jamesjnadeau/watchy-ref-counter/RefCounter/RefMenu.cpp

// ---------------------------------------------------------------------------
// The settings menu.
//
// The shape of this -- a highlighted list, UP and DOWN to move, MENU to
// select, BACK to leave, a set-time screen whose current field blinks, a WiFi
// access point for entering credentials, an NTP sync that reports what it did
// -- follows the reference Watchy firmware, sqfmi/Watchy (MIT licence), by way
// of credit. The code is this project's own; nothing is linked from or copied
// out of that repo.
//
// Deliberate differences from the reference:
//   - no "Show Accelerometer"; nothing on a play clock reads the sensor
//   - no "Vibrate Motor" buzz test; the buzzer proves itself every countdown
//   - "Sync NTP" is only listed once WiFi credentials have been saved, since
//     with none stored it could only ever report a failure
//   - "Sync BT" has no counterpart there at all: the watch advertises the
//     standard Current Time Service and a phone writes the time into it
//   - colours follow DARK_MODE rather than being fixed black on white
//   - actions never redraw the menu themselves; open() owns that
//   - NTP goes through the ESP32 core's SNTP client, not a separate library
//   - the digits reuse this project's seven-segment drawing, not a font
//   - "TZ" and "DST" have no counterpart there; the reference firmware takes
//     its offset from a compile-time constant
// ---------------------------------------------------------------------------

#include "RefMenu.h"

#include <WiFi.h>
#include <WiFiManager.h>

#include "Buttons.h"
#include "Buzzer.h"
#include "RefBleTime.h"
#include "RefDisplay.h"
#include "RefMenuItems.h"
#include "RefPanel.h"
#include "RefSport.h"
#include "RefWifi.h"
#include "RefZone.h"
#include "board.h"
#include "settings.h"

namespace RefMenu {
namespace {

auto &display = RefPanel::display;

const int16_t MENU_ROW_H = 25;

// Rows that fit on the panel at MENU_ROW_H. Both sync rows on offer makes the
// list two rows longer than this, so drawMenu scrolls a window over it, the
// way pickTimeZone does over the zones; strip both conditional rows away and
// it fits exactly.
const uint8_t MENU_VISIBLE = 7;

// Whether the Bluetooth row is worth offering. A build with no BLE, or with
// BT_TIME_SYNC off, leaves it out entirely.
bool btAvailable() { return RefBleTime::supported(); }

// The rows currently on offer, in order, and how many there are. Rebuilt on
// the way in and after every action, because "Setup WiFi" can add or remove
// "Sync NTP" underneath the user.
uint8_t visible[ITEM_COUNT];
uint8_t visibleCount = 0;

// Top of the visible window. Lives outside drawMenu so it survives the redraws
// that follow an action, and is reset in open() so the menu never comes up
// scrolled from last time.
uint8_t menuTop = 0;

// "UTC-5", or "UTC-9:30" if a zone ever needs it.
void formatOffset(char *buf, size_t n, long seconds) {
  const char sign = seconds < 0 ? '-' : '+';
  long mag = seconds < 0 ? -seconds : seconds;
  if (mag > 24L * 3600L) {
    mag = 24L * 3600L; // no real zone is further out, and this bounds the width
  }
  const int hours = (int)(mag / 3600);
  const int mins  = (int)((mag % 3600) / 60);
  if (mins == 0) {
    snprintf(buf, n, "UTC%c%d", sign, hours);
  } else {
    snprintf(buf, n, "UTC%c%d:%02d", sign, hours, mins);
  }
}

enum SetField : int8_t { SET_HOUR, SET_MINUTE, SET_YEAR, SET_MONTH, SET_DAY };

bool pressed(uint8_t pin) { return digitalRead(pin) == BTN_PRESSED_LEVEL; }

void claimButtons() {
  pinMode(PIN_BTN_MENU, INPUT);
  pinMode(PIN_BTN_BACK, INPUT);
  pinMode(PIN_BTN_UP, INPUT);
  pinMode(PIN_BTN_DOWN, INPUT);
}

void beginTextScreen() {
  display.setFullWindow();
  display.fillScreen(THEME_BG);
  display.setFont(&FreeMonoBold9pt7b);
  display.setTextColor(THEME_FG);
  display.setCursor(0, 20);
}

void printTwo(int v) {
  if (v < 10) {
    display.print("0");
  }
  display.print(v);
}

// `slot` is a position in `visible`, not an Item id.
void drawMenu(uint8_t slot, bool partial) {
  // Keep the highlighted row inside the window, and never scroll past the end.
  if (slot < menuTop) {
    menuTop = slot;
  } else if (slot >= menuTop + MENU_VISIBLE) {
    menuTop = (uint8_t)(slot - MENU_VISIBLE + 1);
  }
  if (visibleCount > MENU_VISIBLE &&
      menuTop > (uint8_t)(visibleCount - MENU_VISIBLE)) {
    menuTop = (uint8_t)(visibleCount - MENU_VISIBLE);
  } else if (visibleCount <= MENU_VISIBLE) {
    menuTop = 0;
  }

  display.setFullWindow();
  display.fillScreen(THEME_BG);
  display.setFont(&FreeMonoBold9pt7b);

  char label[ITEM_LABEL_MAX];
  int16_t x1, y1;
  uint16_t w, h;
  for (uint8_t row = 0; row < MENU_VISIBLE && menuTop + row < visibleCount;
       row++) {
    const uint8_t s = (uint8_t)(menuTop + row);
    itemLabel(visible[s], label, sizeof(label));
    const int16_t yPos = MENU_ROW_H + (MENU_ROW_H * row);
    display.setCursor(0, yPos);
    if (s == slot) {
      display.getTextBounds(label, 0, yPos, &x1, &y1, &w, &h);
      display.fillRect(x1 - 1, y1 - 10, DISPLAY_WIDTH, h + 15, THEME_FG);
      display.setTextColor(THEME_BG);
    } else {
      display.setTextColor(THEME_FG);
    }
    display.println(label);
  }
  display.display(partial);
}

void showAbout(RefClock &refClock) {
  beginTextScreen();

  display.print("Ref Counter ");
  display.println(REF_COUNTER_VERSION);
  display.print("Board: ");
  display.println(BOARD_NAME);
  display.print("Batt: ");
  display.print(refClock.batteryVolts(), 2);
  display.println("V");

  struct tm now;
  const bool haveTime = refClock.localNow(now);
  display.print("Now: ");
  if (!haveTime) {
    display.println("not set");
  } else {
    display.print(now.tm_year + 1900);
    display.print("/");
    printTwo(now.tm_mon + 1);
    display.print("/");
    printTwo(now.tm_mday);
    display.print(" ");
    printTwo(now.tm_hour);
    display.print(":");
    printTwo(now.tm_min);
    display.println();
  }

  const time_t nowEpoch = haveTime ? refClock.rtc().epoch() : 0;
  const time_t boot     = refClock.bootEpoch();
  if (boot != 0 && nowEpoch > boot) {
    const uint32_t up = (uint32_t)(nowEpoch - boot);
    display.print("Up: ");
    display.print(up / 86400);
    display.print("d");
    display.print((up % 86400) / 3600);
    display.print("h");
    display.print((up % 3600) / 60);
    display.println("m");
  }

  // Which source last set the clock matters as much as when: an hour out
  // after a Bluetooth sync means the phone's zone and the watch's disagree,
  // which is a different fault from a stale NTP sync.
  const time_t sync = refClock.lastSyncEpoch();
  const char *how   = "";
  switch (refClock.lastSyncSource()) {
  case RefClock::SYNC_NTP: how = " NTP"; break;
  case RefClock::SYNC_BT:  how = " BT"; break;
  default: break;
  }
  if (sync == 0) {
    display.println("Sync: never");
  } else if (nowEpoch > sync) {
    char line[24];
    snprintf(line, sizeof(line), "Sync: %uh ago%s",
             (unsigned)((uint32_t)(nowEpoch - sync) / 3600), how);
    display.println(line);
  }

  const char *rtcName = "none";
  switch (refClock.rtc().kind()) {
  case RefRtc::PCF8563: rtcName = "PCF8563"; break;
  case RefRtc::RV3028:  rtcName = "RV-3028"; break;
  default: break;
  }
  display.print("RTC: ");
  display.println(rtcName);

  // The offset actually in force, which is the only way to confirm from the
  // watch that the daylight saving rule did what was expected of it.
  char offset[12];
  formatOffset(offset, sizeof(offset), refClock.utcOffsetSeconds());
  display.print(RefZone::name(RefZone::index()));
  display.print(" ");
  display.print(refClock.zoneAbbrev());
  display.print(" ");
  display.println(offset);

  display.display(false); // full refresh
}

// The sport picker. Same shape as the zone picker below: a scrolling window of
// rows, MENU to take the highlighted one, BACK to leave the stored one alone,
// and a timeout so a menu opened by accident cannot strand anyone mid-game.
void pickSport() {
  const int16_t ROW_H   = 22;
  const uint8_t VISIBLE = 7;
  const int16_t FIRST_Y = 22;
  const int16_t RULE_Y  = 164;
  const uint8_t total   = RefSport::count();

  uint8_t index = RefSport::index();
  uint8_t top   = index < VISIBLE ? 0 : (uint8_t)(index - VISIBLE + 1);

  claimButtons();
  display.setFullWindow();

  bool first = true;
  uint32_t lastActivity = millis();
  while (millis() - lastActivity < MENU_TIMEOUT_MS) {
    // Keep the highlighted row inside the visible window.
    if (index < top) {
      top = index;
    } else if (index >= top + VISIBLE) {
      top = (uint8_t)(index - VISIBLE + 1);
    }

    display.fillScreen(THEME_BG);
    display.setFont(&FreeMonoBold9pt7b);

    // "Custom    199/199" is the widest row, 17 glyphs of the 18 that fit --
    // Custom is reachable at its ceiling, which none of the fixed presets are.
    char row[24];
    for (uint8_t slot = 0; slot < VISIBLE && top + slot < total; slot++) {
      const uint8_t s       = (uint8_t)(top + slot);
      const int16_t yPos    = FIRST_Y + ROW_H * slot;
      const RefSport::Preset p = RefSport::preset(s);
      snprintf(row, sizeof(row), "%-9s %u/%u", p.name, (unsigned)p.longSeconds,
               (unsigned)p.shortSeconds);

      if (s == index) {
        display.fillRect(0, yPos - 17, DISPLAY_WIDTH, ROW_H - 1, THEME_FG);
        display.setTextColor(THEME_BG);
      } else {
        display.setTextColor(THEME_FG);
      }
      display.setCursor(2, yPos);
      display.print(row);
    }

    display.setTextColor(THEME_FG);
    display.drawFastHLine(0, RULE_Y, DISPLAY_WIDTH, THEME_FG);

    const RefSport::Preset sel = RefSport::preset(index);

    display.setCursor(2, 180);
    display.print(sel.description);

    char counter[10];
    snprintf(counter, sizeof(counter), "%u/%u", (unsigned)(index + 1),
             (unsigned)total);
    // FreeMonoBold9pt7b advances 11 pixels a glyph, so right-aligning is
    // arithmetic rather than a getTextBounds round trip.
    display.setCursor(DISPLAY_WIDTH - 2 - (int16_t)(strlen(counter) * 11), 180);
    display.print(counter);

    // The warning marks, which are the half of a preset the rows have no room
    // for. The final-countdown value is deliberately not here: it is 5 for
    // every fixed preset, so it never tells two of them apart, and the one
    // preset that can change it shows it spelled out on its own editor screen.
    // Three values would need a one-letter label to fit the panel at 199.
    char marks[24];
    snprintf(marks, sizeof(marks), "warn %u/%u",
             (unsigned)sel.warnAtSeconds, (unsigned)sel.warn2AtSeconds);
    display.setCursor(2, 196);
    display.print(marks);

    display.display(!first); // full refresh on the way in, partial to scroll
    first = false;

    // Poll until something happens, so a settled screen is not redrawn on a
    // loop for no reason.
    while (millis() - lastActivity < MENU_TIMEOUT_MS) {
      if (pressed(PIN_BTN_MENU)) {
        RefSport::setIndex(index);
        Buzzer::pulse(BUZZ_CONFIRM_MS);
        Buttons::waitForRelease();
        return;
      }
      if (pressed(PIN_BTN_BACK)) {
        Buttons::waitForRelease();
        return; // leave the stored sport alone
      }
      if (pressed(PIN_BTN_UP)) {
        index = (index == 0) ? (uint8_t)(total - 1) : (uint8_t)(index - 1);
        lastActivity = millis();
        break;
      }
      if (pressed(PIN_BTN_DOWN)) {
        index = (uint8_t)((index + 1) % total);
        lastActivity = millis();
        break;
      }
      delay(BUTTON_POLL_MS);
    }
  }
}

// The zone picker. Eleven zones do not fit on a 200 pixel panel, so this
// scrolls a seven row window and reports the highlighted zone underneath.
void pickTimeZone() {
  const int16_t ROW_H     = 22;
  const uint8_t VISIBLE   = 7;
  const int16_t FIRST_Y   = 22;
  const int16_t RULE_Y    = 164;
  const uint8_t total     = RefZone::count();

  uint8_t index = RefZone::index();
  uint8_t top   = index < VISIBLE ? 0 : (uint8_t)(index - VISIBLE + 1);

  claimButtons();
  display.setFullWindow();

  bool first = true;
  uint32_t lastActivity = millis();
  while (millis() - lastActivity < MENU_TIMEOUT_MS) {
    // Keep the highlighted row inside the visible window.
    if (index < top) {
      top = index;
    } else if (index >= top + VISIBLE) {
      top = (uint8_t)(index - VISIBLE + 1);
    }

    display.fillScreen(THEME_BG);
    display.setFont(&FreeMonoBold9pt7b);

    char row[24], offset[12];
    for (uint8_t slot = 0; slot < VISIBLE && top + slot < total; slot++) {
      const uint8_t z    = (uint8_t)(top + slot);
      const int16_t yPos = FIRST_Y + ROW_H * slot;
      formatOffset(offset, sizeof(offset),
                   RefZone::standardOffsetMinutes(z) * 60L);
      snprintf(row, sizeof(row), "%-8s %s", RefZone::name(z), offset);

      if (z == index) {
        display.fillRect(0, yPos - 17, DISPLAY_WIDTH, ROW_H - 1, THEME_FG);
        display.setTextColor(THEME_BG);
      } else {
        display.setTextColor(THEME_FG);
      }
      display.setCursor(2, yPos);
      display.print(row);
    }

    display.setTextColor(THEME_FG);
    display.drawFastHLine(0, RULE_Y, DISPLAY_WIDTH, THEME_FG);

    // Abbreviations on the left, position in the list on the right. The
    // standard offset is on the row itself, so this is where the reader finds
    // out whether the zone shifts at all.
    char abbrev[20];
    if (RefZone::observesDst(index)) {
      snprintf(abbrev, sizeof(abbrev), "%s/%s", RefZone::standardAbbrev(index),
               RefZone::daylightAbbrev(index));
    } else {
      snprintf(abbrev, sizeof(abbrev), "%s, no DST",
               RefZone::standardAbbrev(index));
    }
    display.setCursor(2, 180);
    display.print(abbrev);

    char counter[10];
    snprintf(counter, sizeof(counter), "%u/%u", (unsigned)(index + 1),
             (unsigned)total);
    // FreeMonoBold9pt7b advances 11 pixels a glyph, so right-aligning is
    // arithmetic rather than a getTextBounds round trip.
    display.setCursor(DISPLAY_WIDTH - 2 - (int16_t)(strlen(counter) * 11), 180);
    display.print(counter);

    display.setCursor(2, 196);
    display.print(RefZone::region(index));

    display.display(!first); // full refresh on the way in, partial to scroll
    first = false;

    // Poll until something happens, so a settled screen is not redrawn on a
    // loop for no reason.
    while (millis() - lastActivity < MENU_TIMEOUT_MS) {
      if (pressed(PIN_BTN_MENU)) {
        RefZone::setIndex(index);
        Buzzer::pulse(BUZZ_CONFIRM_MS);
        Buttons::waitForRelease();
        return;
      }
      if (pressed(PIN_BTN_BACK)) {
        Buttons::waitForRelease();
        return; // leave the stored zone alone
      }
      if (pressed(PIN_BTN_UP)) {
        index = (index == 0) ? (uint8_t)(total - 1) : (uint8_t)(index - 1);
        lastActivity = millis();
        break;
      }
      if (pressed(PIN_BTN_DOWN)) {
        index = (uint8_t)((index + 1) % total);
        lastActivity = millis();
        break;
      }
      delay(BUTTON_POLL_MS);
    }
  }
}

// MENU steps forward through the fields and commits past the last one, BACK
// steps back, UP and DOWN change the value under the cursor. The field being
// edited blinks, which is what tells you where you are.
//
// Times out after MENU_TIMEOUT_MS with nothing pressed, and a timeout leaves
// the clock exactly as it was. This screen repaints twice a second, so one
// opened by accident and then left alone would otherwise hold the watch there
// -- refreshing the panel the whole time -- until the battery went flat.
void setTime(RefClock &refClock) {
  struct tm current;
  if (!refClock.localNow(current)) {
    // Nothing sensible on the clock yet, so start from a fixed point rather
    // than from whatever the chip powered up holding.
    current          = {};
    current.tm_year  = 125; // 2025
    current.tm_mon   = 0;
    current.tm_mday  = 1;
  }

  int hour   = current.tm_hour;
  int minute = current.tm_min;
  int year   = (current.tm_year + 1900) % 100;
  int month  = current.tm_mon + 1;
  int day    = current.tm_mday;

  int8_t field     = SET_HOUR;
  bool   blink     = false;
  // Only true on the MENU-past-last-field path below, so a timeout -- which
  // also falls out of the loop -- can never reach the RTC write at the bottom.
  bool   committed = false;

  claimButtons();
  display.setFullWindow();

  const int16_t pairY = 40;
  const int16_t leftX = 4;
  const int16_t rightX = DISPLAY_WIDTH - RefDisplay::DIGIT_PAIR_W - 4;

  uint32_t lastActivity = millis();
  while (millis() - lastActivity < MENU_TIMEOUT_MS) {
    const bool menuDown = pressed(PIN_BTN_MENU);
    const bool backDown = pressed(PIN_BTN_BACK);
    const bool upDown   = pressed(PIN_BTN_UP);
    const bool downDown = pressed(PIN_BTN_DOWN);
    // Any press counts as activity, even one that turns out to be inert (BACK
    // on the first field): a user still working the buttons is not idle.
    if (menuDown || backDown || upDown || downDown) {
      lastActivity = millis();
    }

    if (menuDown) {
      field++;
      if (field > SET_DAY) {
        committed = true;
        break;
      }
    }
    if (backDown && field != SET_HOUR) {
      field--;
    }

    blink = !blink;

    const int delta = downDown ? 1 : (upDown ? -1 : 0);
    if (delta != 0) {
      blink = true; // never hide the field the user is actively changing
      switch (field) {
      case SET_HOUR:   hour = (hour + delta + 24) % 24; break;
      case SET_MINUTE: minute = (minute + delta + 60) % 60; break;
      case SET_YEAR:   year = (year + delta + 100) % 100; break;
      case SET_MONTH:  month = (month - 1 + delta + 12) % 12 + 1; break;
      case SET_DAY:    day = (day - 1 + delta + 31) % 31 + 1; break;
      default: break;
      }
    }

    display.fillScreen(THEME_BG);
    display.setTextColor(THEME_FG);

    RefDisplay::drawDigitPair(leftX, pairY, (uint8_t)hour,
                              field != SET_HOUR || blink);
    RefDisplay::drawDigitPair(rightX, pairY, (uint8_t)minute,
                              field != SET_MINUTE || blink);
    // Colon between the two pairs.
    display.fillRect(DISPLAY_WIDTH / 2 - 4, pairY + 18, 8, 8, THEME_FG);
    display.fillRect(DISPLAY_WIDTH / 2 - 4, pairY + 40, 8, 8, THEME_FG);

    display.setFont(&FreeMonoBold9pt7b);
    display.setCursor(45, 150);
    display.setTextColor(field == SET_YEAR && !blink ? THEME_BG : THEME_FG);
    display.print(2000 + year);
    display.setTextColor(THEME_FG);
    display.print("/");
    display.setTextColor(field == SET_MONTH && !blink ? THEME_BG : THEME_FG);
    printTwo(month);
    display.setTextColor(THEME_FG);
    display.print("/");
    display.setTextColor(field == SET_DAY && !blink ? THEME_BG : THEME_FG);
    printTwo(day);

    display.setTextColor(THEME_FG);
    display.setCursor(6, 185);
    display.print("MENU next  BACK prev");

    display.display(true); // partial refresh
  }

  if (!committed) {
    return; // timed out part way through; the clock keeps the time it had
  }

  struct tm t = {};
  t.tm_year   = 100 + year; // years since 1900
  t.tm_mon    = month - 1;
  t.tm_mday   = day;
  t.tm_hour   = hour;
  t.tm_min    = minute;
  t.tm_sec    = 0;
  // What was typed is local time; the RTC holds UTC, so this converts.
  refClock.setLocal(t);
}

enum CustomField : int8_t {
  CF_LONG,
  CF_SHORT,
  CF_WARN,
  CF_WARN2,
  CF_FINAL,
  CF_COUNT,
};

const char *customFieldLabel(int8_t f) {
  switch (f) {
  case CF_LONG:  return "Long";
  case CF_SHORT: return "Short";
  case CF_WARN:  return "Warn 1";
  case CF_WARN2: return "Warn 2";
  default:       return "Final";
  }
}

// Edit the Custom preset's five numbers. MENU steps forward through the fields
// and commits past the last one, BACK steps back, UP and DOWN change the value
// under the cursor, and the field being edited blinks -- the same interaction
// as setTime above, deliberately -- MENU_TIMEOUT_MS bail-out included, so a
// screen opened by accident cannot strand the watch on it mid-game. This one
// is menu row 2, directly under where the menu opens, so that matters here.
//
// Values are text rather than seven-segment digits: five labelled rows are far
// more readable than five bare numbers, and it keeps new segment geometry out
// of the menu.
//
// This does not select Custom. The user picks it from the Sport screen, which
// keeps "edit" and "use" separate the way the zone picker keeps them.
void editCustom() {
  const RefSport::Preset c = RefSport::custom();
  uint16_t value[CF_COUNT] = {c.longSeconds, c.shortSeconds, c.warnAtSeconds,
                              c.warn2AtSeconds, c.finalCountdownFrom};

  int8_t field     = CF_LONG;
  bool   blink     = false;
  // Only true on the MENU-past-last-field path below, so a timeout -- which
  // also falls out of the loop -- can never reach the commit at the bottom.
  bool   committed = false;

  claimButtons();
  display.setFullWindow();

  // No delay in this loop and no debounce: the partial refresh at the bottom
  // takes most of half a second, which is what paces it. Same as setTime.
  uint32_t lastActivity = millis();
  while (millis() - lastActivity < MENU_TIMEOUT_MS) {
    const bool menuDown = pressed(PIN_BTN_MENU);
    const bool backDown = pressed(PIN_BTN_BACK);
    const bool upDown   = pressed(PIN_BTN_UP);
    const bool downDown = pressed(PIN_BTN_DOWN);
    // Any press counts as activity, even one that turns out to be inert (BACK
    // on the first field): a user still working the buttons is not idle.
    if (menuDown || backDown || upDown || downDown) {
      lastActivity = millis();
    }

    if (menuDown) {
      field++;
      if (field >= CF_COUNT) {
        committed = true;
        break;
      }
    }
    if (backDown && field != CF_LONG) {
      field--;
    }

    blink = !blink;

    const int delta = downDown ? 1 : (upDown ? -1 : 0);
    if (delta != 0) {
      blink = true; // never hide the field the user is actively changing
      // The two clocks bottom out at 1; a mark of 0 means off, so those wrap
      // through zero.
      const int lo = (field == CF_LONG || field == CF_SHORT)
                         ? (int)RefSport::MIN_CLOCK_SECONDS
                         : 0;
      int v = (int)value[field] + delta;
      if (v > (int)RefSport::MAX_SECONDS) {
        v = lo;
      } else if (v < lo) {
        v = (int)RefSport::MAX_SECONDS;
      }
      value[field] = (uint16_t)v;
    }

    display.fillScreen(THEME_BG);
    display.setFont(&FreeMonoBold9pt7b);

    display.setTextColor(THEME_FG);
    display.setCursor(2, 20);
    display.print("EDIT CUSTOM");
    display.drawFastHLine(0, 28, DISPLAY_WIDTH, THEME_FG);

    for (int8_t f = 0; f < CF_COUNT; f++) {
      const int16_t yPos = 52 + 24 * f;

      display.setTextColor(THEME_FG);
      display.setCursor(2, yPos);
      display.print(customFieldLabel(f));

      char num[8];
      snprintf(num, sizeof(num), "%3u", (unsigned)value[f]);
      // Three glyphs at 11 pixels each, right-aligned against the edge.
      display.setCursor(DISPLAY_WIDTH - 2 - 33, yPos);
      display.setTextColor(f == field && !blink ? THEME_BG : THEME_FG);
      display.print(num);
    }

    display.setTextColor(THEME_FG);
    display.setCursor(2, 194);
    display.print("MENU/BACK to move");

    display.display(true); // partial refresh
  }

  // A timeout falls out of the loop above too, so this only fires on the
  // MENU-past-last-field path -- a stale in-progress edit is never persisted.
  if (committed) {
    RefSport::setCustom(value[CF_LONG], value[CF_SHORT], value[CF_WARN],
                        value[CF_WARN2], value[CF_FINAL]);
    Buzzer::pulse(BUZZ_CONFIRM_MS);
  }
}

void portalCallback(WiFiManager *) {
  beginTextScreen();
  display.setCursor(0, 30);
  display.println("Connect to");
  display.print("SSID: ");
  display.println(WIFI_AP_NAME);
  display.print("IP: ");
  display.println(WiFi.softAPIP());
  display.println("MAC:");
  display.println(WiFi.softAPmacAddress().c_str());
  display.display(false); // full refresh
}

void setupWifi() {
  WiFiManager wifiManager;
  wifiManager.resetSettings();
  wifiManager.setTimeout(WIFI_AP_TIMEOUT_S);
  wifiManager.setAPCallback(portalCallback);

  beginTextScreen();
  // resetSettings() above wiped whatever was stored, so the flag has to track
  // the outcome both ways: a setup that fails or times out really has left the
  // watch with no credentials, and "Sync NTP" goes away again with them.
  const bool ok = wifiManager.autoConnect(WIFI_AP_NAME);
  RefWifi::setConfigured(ok);
  if (!ok) {
    display.println("Setup failed or");
    display.println("timed out.");
  } else {
    display.println("Connected to:");
    display.println(WiFi.SSID());
    display.println("Local IP:");
    display.println(WiFi.localIP());
  }
  display.display(false); // full refresh

  WiFi.mode(WIFI_OFF);
}

void showSyncNTP(RefClock &refClock) {
  beginTextScreen();
  display.setCursor(0, 30);
  display.println("Syncing NTP...");
  display.print("Zone: ");
  display.println(RefZone::name(RefZone::index()));
  display.display(false); // full refresh

  bool connected = WiFi.begin() != WL_CONNECT_FAILED &&
                   WiFi.waitForConnectResult() == WL_CONNECTED;
  if (!connected) {
    display.println("WiFi not configured");
  } else if (refClock.syncFromNtp()) {
    display.println("Sync OK. Time is:");
    struct tm now;
    if (refClock.localNow(now)) {
      display.print(now.tm_year + 1900);
      display.print("/");
      printTwo(now.tm_mon + 1);
      display.print("/");
      printTwo(now.tm_mday);
      display.print(" ");
      printTwo(now.tm_hour);
      display.print(":");
      printTwo(now.tm_min);
      display.print(" ");
      display.println(refClock.zoneAbbrev());
    }
  } else {
    display.println("Sync failed");
  }
  WiFi.disconnect(true);
  WiFi.mode(WIFI_OFF);

  display.display(true); // partial refresh
  delay(3000);
}

// The Bluetooth sync screen.
//
// Unlike "Sync NTP", which blocks inside one call and reports afterwards,
// this one has to wait with the panel up: the other half of it is a phone in
// somebody's hand. So it says what it is waiting for, notices a phone
// arriving, and takes BACK for an answer.
//
// It repaints only when that state changes -- waiting, connected, done --
// rather than counting a timer down on screen. Every repaint is a partial
// refresh of the whole panel, and a second-by-second countdown would spend
// the whole window refreshing e-paper for no information anyone needs.
void showSyncBluetooth(RefClock &refClock) {
  // Bring the radio up first, so the panel is painted once with whatever
  // actually happened rather than showing a "starting" screen for 2.6s.
  const bool up = RefBleTime::begin();

  beginTextScreen();
  display.setCursor(0, 30);
  if (!up) {
    display.println("Bluetooth failed");
    display.println("to start.");
    display.display(false); // full refresh
    delay(3000);
    return;
  }

  // Give a phone that reads the characteristics something true to read.
  // Skipped when the clock has never been set: there is nothing to publish.
  struct tm local;
  if (refClock.localNow(local)) {
    refClock.publishBleTime(local);
  }

  display.println("Sync BT");
  display.println();
  display.println("Waiting for");
  display.println("phone. Send the");
  display.println("time to:");
  display.println(RefBleTime::deviceName());
  display.println();
  display.println("BACK to cancel");
  display.display(false); // full refresh

  claimButtons();

  bool connected = false;
  bool cancelled = false;
  bool received  = false;
  RefCtsTime::Stamp stamp;
  RefCtsTime::clear(stamp);

  const uint32_t deadline = millis() + BT_SYNC_TIMEOUT_MS;
  while ((int32_t)(millis() - deadline) < 0) {
    if (RefBleTime::take(stamp)) {
      received = true;
      break;
    }
    if (pressed(PIN_BTN_BACK)) {
      cancelled = true;
      break;
    }
    // A phone connecting is worth showing: it is the half of the exchange the
    // watch can confirm, and it tells you to look at the phone rather than at
    // the watch. Plenty of phones connect, look around and leave again
    // without writing anything, so this is not a sync in itself.
    const bool nowConnected = RefBleTime::connected();
    if (nowConnected != connected) {
      connected = nowConnected;
      beginTextScreen();
      display.setCursor(0, 30);
      display.println("Sync BT");
      display.println();
      if (connected) {
        display.println("Phone connected.");
        display.println("Waiting for the");
        display.println("time...");
      } else {
        display.println("Phone left.");
        display.println("Waiting again");
        display.println("as:");
        display.println(RefBleTime::deviceName());
      }
      display.println();
      display.println("BACK to cancel");
      display.display(true); // partial refresh
    }
    delay(BUTTON_POLL_MS);
  }

  // Radio down before the clock is written and the result drawn: neither
  // needs it, and a several-second e-paper refresh with the transmitter still
  // up is battery spent for nothing.
  RefBleTime::end();

  if (cancelled) {
    return; // open() redraws the menu; nothing was changed to report
  }

  beginTextScreen();
  display.setCursor(0, 30);

  if (!received) {
    display.println("No time received.");
    display.println();
    display.println("Is the phone app");
    display.println("set to sync time?");
    // A window that ran its full length and found nothing is a real attempt,
    // so it counts against the automatic schedule's minimum interval the same
    // way a failed NTP sync does. A cancelled one is not, which is why this
    // sits below the early return above.
    refClock.noteSyncAttempt();
  } else if (!refClock.applyBleStamp(stamp)) {
    display.println("Clock write");
    display.println("failed.");
  } else {
    Buzzer::pulse(BUZZ_CONFIRM_MS);
    display.println("Sync OK. Time is:");
    struct tm now;
    if (refClock.localNow(now)) {
      display.print(now.tm_year + 1900);
      display.print("/");
      printTwo(now.tm_mon + 1);
      display.print("/");
      printTwo(now.tm_mday);
      display.print(" ");
      printTwo(now.tm_hour);
      display.print(":");
      printTwo(now.tm_min);
      display.print(" ");
      display.println(refClock.zoneAbbrev());
    }
    display.println();
    // Worth saying which zone the conversion used. If the watch ends up an
    // hour out, this line is the difference between a phone that sent its own
    // offset and one that left the watch to assume its TZ setting.
    if (stamp.haveOffset) {
      display.println("Zone: from phone");
    } else {
      display.print("Zone: ");
      display.println(RefZone::name(RefZone::index()));
    }
  }

  display.display(true); // partial refresh
  delay(3000);
}

// Hold a result screen until the user backs out of it.
void waitForBack() {
  pinMode(PIN_BTN_BACK, INPUT);
  const uint32_t deadline = millis() + MENU_TIMEOUT_MS;
  while ((int32_t)(millis() - deadline) < 0) {
    if (pressed(PIN_BTN_BACK)) {
      break;
    }
    delay(BUTTON_POLL_MS);
  }
  Buttons::waitForRelease();
}

} // namespace

void open(RefClock &refClock) {
  // The hold that opened the menu is still down; without this it would land as
  // an immediate selection of the first entry.
  Buttons::waitForRelease();

  visibleCount = buildVisible(RefWifi::configured(), btAvailable(), visible);
  uint8_t slot = 0;
  menuTop = 0;
  drawMenu(slot, false);
  claimButtons();

  uint32_t lastActivity = millis();
  while (millis() - lastActivity < MENU_TIMEOUT_MS) {
    if (pressed(PIN_BTN_MENU)) {
      Buttons::waitForRelease();
      const uint8_t item = visible[slot];
      bool holdResult = false;
      // The DST switch never leaves the menu, so it gets the quick partial
      // redraw rather than the 2.6s full one every other entry earns.
      bool quickRedraw = false;
      switch (item) {
      case ITEM_ABOUT:    showAbout(refClock); holdResult = true; break;
      case ITEM_SYNC:     showSyncNTP(refClock); break;
      case ITEM_SYNC_BT:  showSyncBluetooth(refClock); break;
      case ITEM_ZONE:     pickTimeZone(); break;
      case ITEM_DST:
        RefZone::setDstAuto(!RefZone::dstAuto());
        Buzzer::pulse(BUZZ_CONFIRM_MS);
        quickRedraw = true;
        break;
      case ITEM_SET_TIME: setTime(refClock); break;
      case ITEM_WIFI:     setupWifi(); holdResult = true; break;
      case ITEM_SPORT:       pickSport(); break;
      case ITEM_EDIT_CUSTOM: editCustom(); break;
      default: break;
      }
      if (holdResult) {
        waitForBack();
      }
      Buttons::waitForRelease();
      claimButtons();
      // Setup WiFi can make "Sync NTP" appear above it, which moves that row
      // and every row below it down a slot, so the highlight follows the item
      // the user just ran rather than the slot number it used to sit at.
      visibleCount = buildVisible(RefWifi::configured(), btAvailable(), visible);
      const int8_t back = slotOf(visible, visibleCount, item);
      slot = back >= 0 ? (uint8_t)back : 0;
      drawMenu(slot, quickRedraw);
      lastActivity = millis();
    } else if (pressed(PIN_BTN_BACK)) {
      break; // out of the menu entirely
    } else if (pressed(PIN_BTN_UP)) {
      slot = (slot == 0) ? (uint8_t)(visibleCount - 1) : (uint8_t)(slot - 1);
      drawMenu(slot, true);
      lastActivity = millis();
    } else if (pressed(PIN_BTN_DOWN)) {
      slot = (uint8_t)((slot + 1) % visibleCount);
      drawMenu(slot, true);
      lastActivity = millis();
    }
  }

  Buttons::waitForRelease();
  // The loop above read the pins raw. Re-seed the debounce state so a button
  // still settling is not mistaken for a fresh press by the main loop.
  Buttons::resync();
}

} // namespace RefMenu
