jamesjnadeau/watchy-ref-counter/RefCounter/RefDisplay.cpp

#include "RefDisplay.h"

#include <ctype.h>

#include "Buttons.h"
#include "RefPanel.h"
#include "RefSegments.h"
#include "RefSport.h"
#include "board.h"
#include "settings.h"

// RefSegments and RefSport each define their own ceiling so neither has to
// depend on the other. This is the one place both are visible, so it is where
// a divergence gets caught -- at compile time rather than as a silently
// clamped countdown.
static_assert(RefSport::MAX_SECONDS <= SEG_MAX_VALUE,
              "a preset could hold a value the display cannot draw");

extern const uint16_t THEME_FG = DARK_MODE ? GxEPD_WHITE : GxEPD_BLACK;
extern const uint16_t THEME_BG = DARK_MODE ? GxEPD_BLACK : GxEPD_WHITE;

namespace RefDisplay {
namespace {

auto &display = RefPanel::display;

const uint16_t &FG = THEME_FG;
const uint16_t &BG = THEME_BG;

// --- Layout, in pixels on the 200x200 panel --------------------------------
const int16_t SCREEN_W = DISPLAY_WIDTH;

const int16_t HEADER_BASELINE = 26;
const int16_t HEADER_RULE_Y   = 36;

const int16_t BIG_Y  = 44;  // top of the large countdown (RUNNING / EXPIRED)
const int16_t ROW1_Y = 44;  // top of the upper value on the idle screen
const int16_t ROW2_Y = 106; // top of the lower value on the idle screen

const int16_t FOOTER_RULE_Y   = 166;
const int16_t FOOTER_BASELINE = 188;

const int16_t BATT_X = 166;
const int16_t BATT_Y = 14;
const int16_t BATT_W = 26;
const int16_t BATT_H = 12;

// The header strip, refreshed on its own when the minute rolls over. Covers
// the clock, the battery gauge and the rule underneath them.
const int16_t HEADER_WIN_X = 0;
const int16_t HEADER_WIN_Y = 0;
const int16_t HEADER_WIN_W = 200;
const int16_t HEADER_WIN_H = 40;

// The window refreshed on each tick. It has to cover the widest the countdown
// can get, which is 199 in STYLE_BIG: a skinny hundreds bar at x 6 out to the
// right edge of the ones digit at x 193. GxEPD2 rounds x and w out to a
// multiple of 8 regardless, so this is the full panel width rather than a
// nearly-full one pretending to be tighter.
const int16_t DIGITS_WIN_X = 0;
const int16_t DIGITS_WIN_Y = 40;
const int16_t DIGITS_WIN_W = 200;
const int16_t DIGITS_WIN_H = 124;

// --- Seven segment digits --------------------------------------------------
// Drawn from rectangles rather than a font, so the exact bounding box of the
// countdown is known at compile time. That is what makes the partial window
// above safe to hard-code, and it drops the 14KB DSEG7 font from the build.
//
//     --a--
//    |     |
//    f     b
//    |     |
//     --g--
//    |     |
//    e     c
//    |     |
//     --d--

const SegStyle STYLE_BIG   = {70, 116, 15, 16}; // 156 x 116 for two digits
const SegStyle STYLE_SMALL = {32, 52, 8, 8};    // 72 x 52 for two digits

// Which segments are lit for each digit. Bit order a,b,c,d,e,f,g.
const uint8_t SEG_A = 0x01, SEG_B = 0x02, SEG_C = 0x04, SEG_D = 0x08,
              SEG_E = 0x10, SEG_F = 0x20, SEG_G = 0x40;

const uint8_t DIGIT_SEGMENTS[10] = {
    /* 0 */ SEG_A | SEG_B | SEG_C | SEG_D | SEG_E | SEG_F,
    /* 1 */ SEG_B | SEG_C,
    /* 2 */ SEG_A | SEG_B | SEG_G | SEG_E | SEG_D,
    /* 3 */ SEG_A | SEG_B | SEG_G | SEG_C | SEG_D,
    /* 4 */ SEG_F | SEG_G | SEG_B | SEG_C,
    /* 5 */ SEG_A | SEG_F | SEG_G | SEG_C | SEG_D,
    /* 6 */ SEG_A | SEG_F | SEG_G | SEG_E | SEG_C | SEG_D,
    /* 7 */ SEG_A | SEG_B | SEG_C,
    /* 8 */ SEG_A | SEG_B | SEG_C | SEG_D | SEG_E | SEG_F | SEG_G,
    /* 9 */ SEG_A | SEG_B | SEG_C | SEG_D | SEG_F | SEG_G,
};

void drawDigit(int16_t x, int16_t y, uint8_t value, const SegStyle &s,
               uint16_t colour) {
  const uint8_t on = DIGIT_SEGMENTS[value % 10];
  const SegRows r = layoutRows(s);

  const int16_t t    = s.t;
  const int16_t barW = s.w - 2 * t;   // length of the horizontal bars
  const int16_t right = x + s.w - t;

  if (on & SEG_A) display.fillRect(x + t, y, barW, t, colour);
  if (on & SEG_B) display.fillRect(right, y + r.upY, t, r.upH, colour);
  if (on & SEG_C) display.fillRect(right, y + r.lowY, t, r.lowH, colour);
  if (on & SEG_D) display.fillRect(x + t, y + s.h - t, barW, t, colour);
  if (on & SEG_E) display.fillRect(x, y + r.lowY, t, r.lowH, colour);
  if (on & SEG_F) display.fillRect(x, y + r.upY, t, r.upH, colour);
  if (on & SEG_G) display.fillRect(x + t, y + r.midY, barW, t, colour);
}

void drawPair(int16_t x, int16_t y, uint16_t value, const SegStyle &s,
              uint16_t colour) {
  if (value > 99) {
    value = 99;
  }
  drawDigit(x, y, (uint8_t)(value / 10), s, colour);
  drawDigit(x + s.w + s.gap, y, (uint8_t)(value % 10), s, colour);
}

// The skinny leading "1": segments b and c only, at the same heights drawDigit
// puts them, but one thickness wide instead of a whole digit.
void drawOneBar(int16_t x, int16_t y, const SegStyle &s, uint16_t colour) {
  const SegRows r = layoutRows(s);
  const int16_t t = s.t;

  display.fillRect(x, y + r.upY, t, r.upH, colour);
  display.fillRect(x, y + r.lowY, t, r.lowH, colour);
}

// A countdown value, 0..199, centred horizontally. Where each glyph goes is
// RefSegments' decision, so it can be checked on a host.
void drawCount(uint16_t value, int16_t y, const SegStyle &s, uint16_t colour) {
  const CountLayout l = layoutCount(value, s, SCREEN_W);
  if (l.hundreds) {
    drawOneBar(l.oneX, y, s, colour);
  }
  drawDigit(l.tensX, y, l.tens, s, colour);
  drawDigit(l.onesX, y, l.ones, s, colour);
}

float batteryVolts() {
  return (analogReadMilliVolts(PIN_BATT_ADC) / 1000.0f) * BATT_DIVIDER;
}

// Draw `text` horizontally centred on `centreX`, at the given baseline.
void printCentred(const char *text, int16_t baselineY, int16_t centreX = SCREEN_W / 2) {
  int16_t x1, y1;
  uint16_t w, h;
  display.getTextBounds(text, 0, baselineY, &x1, &y1, &w, &h);
  // x1 is where the glyphs actually start when the cursor sits at 0, which for
  // a custom font is rarely 0. Subtract it so the ink lands centred, not the
  // cursor.
  display.setCursor(centreX - (int16_t)(w / 2) - x1, baselineY);
  display.print(text);
}

void drawBattery() {
  const float v = batteryVolts();
  float pct = (v - BATT_MIN_V) / (BATT_MAX_V - BATT_MIN_V);
  pct = pct < 0.0f ? 0.0f : (pct > 1.0f ? 1.0f : pct);

  display.drawRect(BATT_X, BATT_Y, BATT_W, BATT_H, FG);
  display.fillRect(BATT_X + BATT_W, BATT_Y + 3, 3, BATT_H - 6, FG);

  const int16_t fill = (int16_t)((BATT_W - 4) * pct);
  if (fill > 0) {
    display.fillRect(BATT_X + 2, BATT_Y + 2, fill, BATT_H - 4, FG);
  }
}

void drawHeader(const View &v) {
  char clock[8];
  if (!v.clockValid) {
    snprintf(clock, sizeof(clock), "--:--");
  } else if (CLOCK_24_HOUR) {
    snprintf(clock, sizeof(clock), "%02u:%02u", v.hour, v.minute);
  } else {
    uint8_t h = v.hour % 12;
    if (h == 0) {
      h = 12;
    }
    snprintf(clock, sizeof(clock), "%u:%02u", h, v.minute);
  }

  display.setFont(&FreeMonoBold9pt7b);
  display.setCursor(4, HEADER_BASELINE);
  display.print(clock);

  drawBattery();
  display.drawFastHLine(0, HEADER_RULE_Y, SCREEN_W, FG);
}

// A solid triangle at the right edge, pointing at the button that starts the
// value on this row.
void drawRowMarker(int16_t rowY, const SegStyle &s) {
  const int16_t cy = rowY + s.h / 2;
  display.fillTriangle(SCREEN_W - 4, cy, SCREEN_W - 16, cy - 8, SCREEN_W - 16,
                       cy + 8, FG);
}

void drawBody(const View &v) {
  if (v.state == STATE_IDLE) {
    // Stack both clocks so they line up with the two right-hand buttons.
    const RefSport::Preset p = RefSport::active();
    drawCount(p.longSeconds, ROW1_Y, STYLE_SMALL, FG);
    drawRowMarker(ROW1_Y, STYLE_SMALL);
    drawCount(p.shortSeconds, ROW2_Y, STYLE_SMALL, FG);
    drawRowMarker(ROW2_Y, STYLE_SMALL);
    return;
  }
  drawCount(v.secondsLeft, BIG_Y, STYLE_BIG, FG);
}

void drawFooter(const View &v) {
  // Room for the longest preset name plus its terminator.
  static char sportUpper[12];
  const char *hint;

  switch (v.state) {
  case STATE_RUNNING:
    hint = "BTM LEFT = CLEAR";
    break;
  case STATE_EXPIRED:
    hint = "TIME EXPIRED";
    break;
  default: {
    // On the ready screen the footer says which preset is loaded. That is the
    // thing worth checking before a game; "hold to start" is in the manual.
    const char *name = RefSport::active().name;
    size_t i = 0;
    for (; name[i] != '\0' && i < sizeof(sportUpper) - 1; i++) {
      sportUpper[i] = (char)toupper((unsigned char)name[i]);
    }
    sportUpper[i] = '\0';
    hint = sportUpper;
    break;
  }
  }

  display.drawFastHLine(0, FOOTER_RULE_Y, SCREEN_W, FG);
  display.setFont(&FreeMonoBold9pt7b);
  printCentred(hint, FOOTER_BASELINE);
}

const SegStyle STYLE_MED = {40, 66, 10, 10};

} // namespace

extern const int16_t DIGIT_PAIR_W = STYLE_MED.w * 2 + STYLE_MED.gap;
extern const int16_t DIGIT_PAIR_H = STYLE_MED.h;

void drawDigitPair(int16_t x, int16_t y, uint8_t value, bool lit) {
  drawPair(x, y, value, STYLE_MED, lit ? THEME_FG : THEME_BG);
}

// Handed to GxEPD2 and called over and over while the panel is busy. The delay
// is what the driver would have done here on its own; it keeps the wait from
// becoming a spin on a watch that is trying to save its battery.
static void busyPoll(const void *) {
  Buttons::poll();
  delay(1);
}

void begin() {
  RefPanel::begin();
  display.setTextColor(FG);
  display.setTextWrap(false);
  // GxEPD2 sits in a busy-wait for the whole of every refresh -- around 300ms
  // for a window, 2.6s for a full one -- and left alone it spends that time
  // doing nothing. Polling the buttons there instead means a hold begun during
  // a refresh is already registered, with its true start time, by the moment
  // the refresh returns.
  display.epd2.setBusyCallback(busyPoll);
}

void paint(const View &v) {
  display.setFullWindow();
  display.fillScreen(BG);
  display.setTextColor(FG);

  drawHeader(v);
  drawBody(v);
  drawFooter(v);
}

void render(const View &v, bool full) {
  paint(v);
  // GxEPD2 takes "partial refresh?" here, so a full refresh is display(false).
  display.display(!full);
}

void renderHeader(const View &v) {
  display.setTextColor(FG);
  display.fillRect(HEADER_WIN_X, HEADER_WIN_Y, HEADER_WIN_W, HEADER_WIN_H, BG);
  drawHeader(v);
  display.displayWindow(HEADER_WIN_X, HEADER_WIN_Y, HEADER_WIN_W, HEADER_WIN_H);
}

void renderDigits(const View &v) {
  display.setTextColor(FG);
  display.fillRect(DIGITS_WIN_X, DIGITS_WIN_Y, DIGITS_WIN_W, DIGITS_WIN_H, BG);
  drawCount(v.secondsLeft, BIG_Y, STYLE_BIG, FG);
  display.displayWindow(DIGITS_WIN_X, DIGITS_WIN_Y, DIGITS_WIN_W, DIGITS_WIN_H);
}

void renderSleeping() {
  display.setFullWindow();
  display.fillScreen(BG);
  display.setTextColor(FG);

  display.setFont(&FreeMonoBold18pt7b);
  printCentred("SLEEPING", 110);

  display.setFont(&FreeMonoBold9pt7b);
  printCentred("TOP LEFT TO WAKE", 150);

  display.display(false);
}

void hibernate() { display.hibernate(); }

} // namespace RefDisplay
